v9938/MSX0_USBKEYBOARD/AssemblyManual/img/img019.jpg

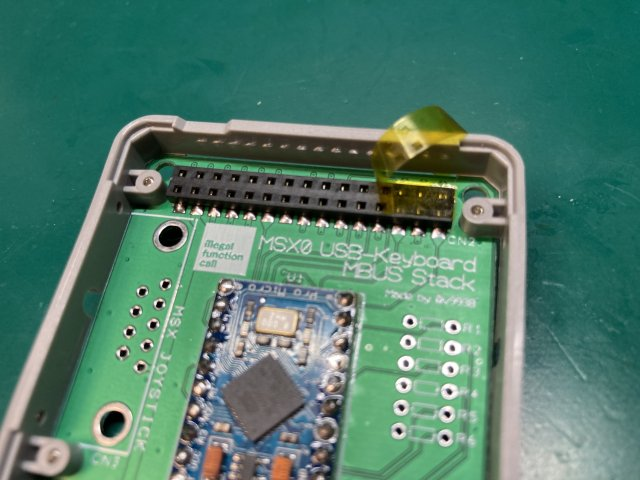
AssemblyManual/img/img019.jpg
