v9938/MSX0_USBKEYBOARD/AssemblyManual/img/img026.png

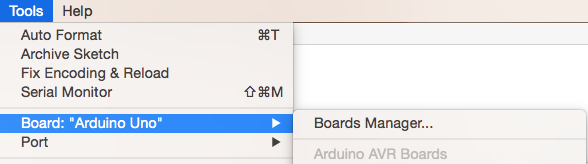
AssemblyManual/img/img026.png
